MacNite/HiveScale/pcb-design/pictures/PCB_V0_Vin_fix_C.jpg

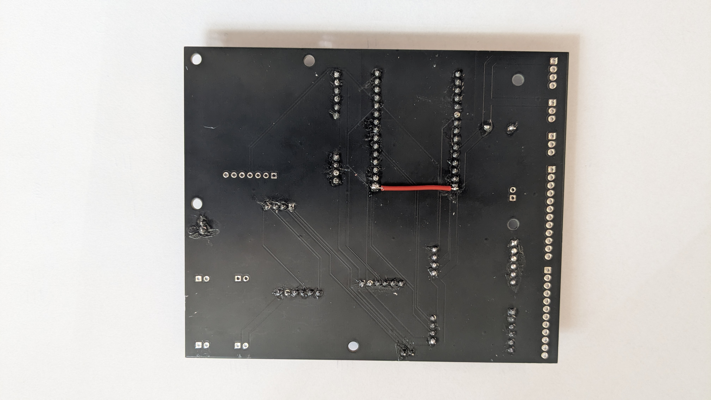
pcb-design/pictures/PCB_V0_Vin_fix_C.jpg
