MacNite/HiveScale/firmware/include/device_prefs.h

// device_prefs.h — NVS (Preferences) seeding, loading, saving and WiFi
// credential management.
#pragma once

#include <Arduino.h>

String prefString(const char* key, const char* fallback = "");
void putPrefString(const char* key, const String& value);
String wifiSsidKey(int index);
String wifiPassKey(int index);

void seedPrefsFromSecretsIfNeeded();
void loadConfigFromPrefs();
void saveScaleConfig();
void markClaimRegistered();

int getWifiCount();
bool saveWifiNetwork(int index, const String& ssid, const String& pass);
void clearWifiCredentials();
void factoryResetPreferences();
